wyolum/morseKEY/kicad/data/Morse Code USB Keyboard Mk II - mitxela.com_files/MorseUSB3.jpg

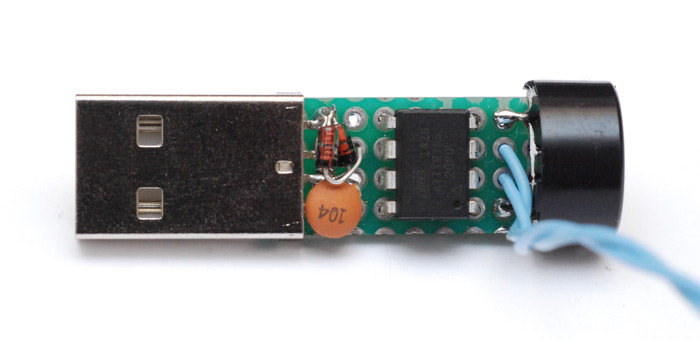
kicad/data/Morse Code USB Keyboard Mk II - mitxela.com_files/MorseUSB3.jpg
