wyolum/morseKEY/kicad/3d/archive/trimpot_vert.step

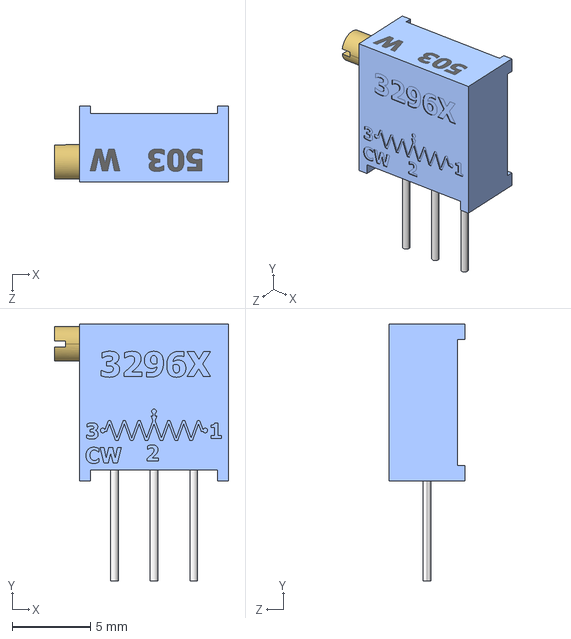
[picture p25: CAD file, 2017-01-30, an earlier design]
kicad/3d/archive/trimpot_vert.step
11.1 x 16.4 x 4.83 mm
