wyolum/morseKEY/kicad/3d/archive/cap_elco_ra.step

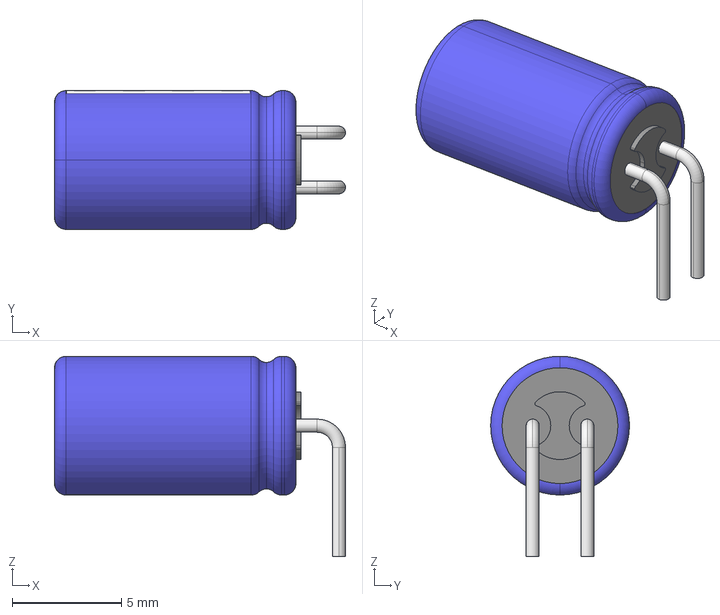
[picture p26: CAD file, 2017-01-30, an earlier design]
kicad/3d/archive/cap_elco_ra.step
13.3 x 6.35 x 9.18 mm
