wyolum/morseKEY/fabricate/renders/morsekey_enc_04.png

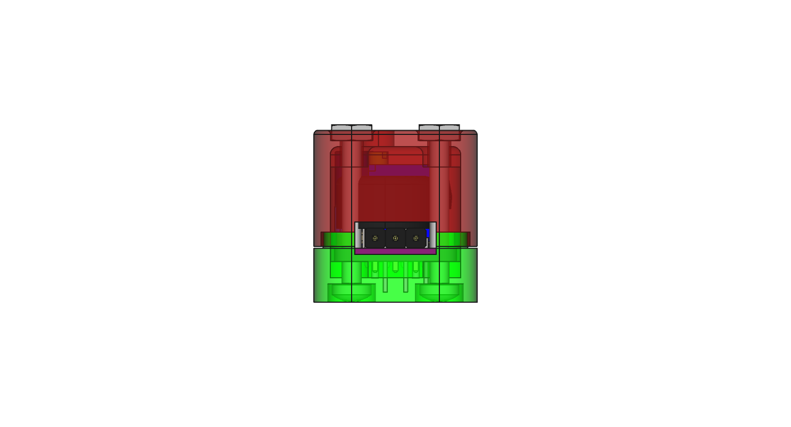
fabricate/renders/morsekey_enc_04.png
