wyolum/morseKEY/kicad/data/Morse Code USB Keyboard Mk II - mitxela.com_files/USB_HID_install.png

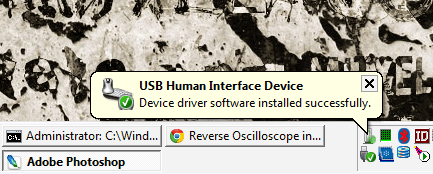
kicad/data/Morse Code USB Keyboard Mk II - mitxela.com_files/USB_HID_install.png
